FEASTorg/Slice_RLHT/firmware/include/config.h

#ifndef CONFIG_H
#define CONFIG_H

#ifndef RLHT_HW_GEN
#define RLHT_HW_GEN 2
#endif

// Bus address is independent of hardware generation.
// Override with a build flag: -DI2C_ADR=<addr>
#ifndef I2C_ADR
#define I2C_ADR 10
#endif

#ifdef SLICE_DEBUG

#define SLICE_DEBUG_PRINT(...) \
    Serial.print(__VA_ARGS__)

#define SLICE_DEBUG_PRINTLN(...) \
    Serial.println(__VA_ARGS__)

#else
#define SLICE_DEBUG_PRINT(...)
#define SLICE_DEBUG_PRINTLN(...)
#endif

#endif // CONFIG_H
