FEASTorg/Slice_RLHT/firmware/RLHT_gen2/config.h

#ifndef CONFIG_H
#define CONFIG_H

// Define the I2C address for this SLICE device
#define I2C_ADR 10
#define TYPE_ID 1 // SLICE type ID for RLHT!!!

#define version "1.0.0" // firmware version, update when making changes

// Uncomment to enable additional debugging messages:
#define SLICE_DEBUG 1

#ifdef SLICE_DEBUG

#define SLICE_DEBUG_PRINT(...) \
    Serial.print(__VA_ARGS__)

#define SLICE_DEBUG_PRINTLN(...) \
    Serial.println(__VA_ARGS__)

#else
#define SLICE_DEBUG_PRINT(...)
#define SLICE_DEBUG_PRINTLN(...)
#endif

#endif // CONFIG_H
